ellemenno/pinwheel-system/wing5-2.stl

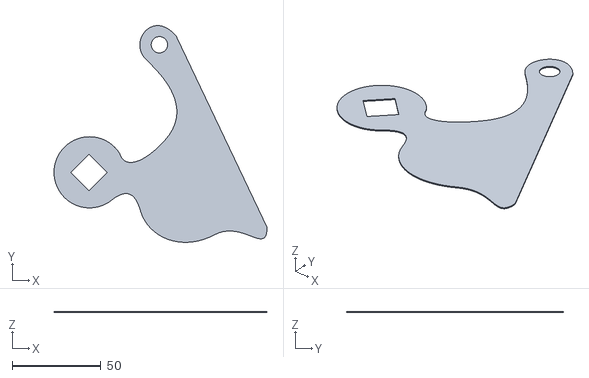
[picture p14: CAD file, 2023-04-02]
wing5-2.stl
119.9 x 122.0 x 0.5
