ellemenno/pinwheel-system/housing+fin.stl

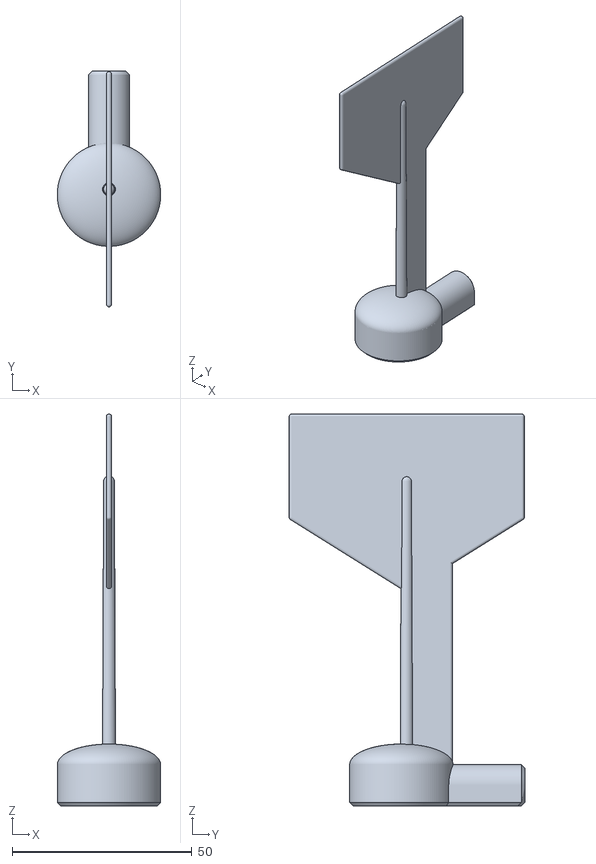
[picture p15: CAD file, 2023-04-02]
housing+fin.stl
28.8 x 65.6 x 109.1
