ellemenno/pinwheel-system/pin6.stl

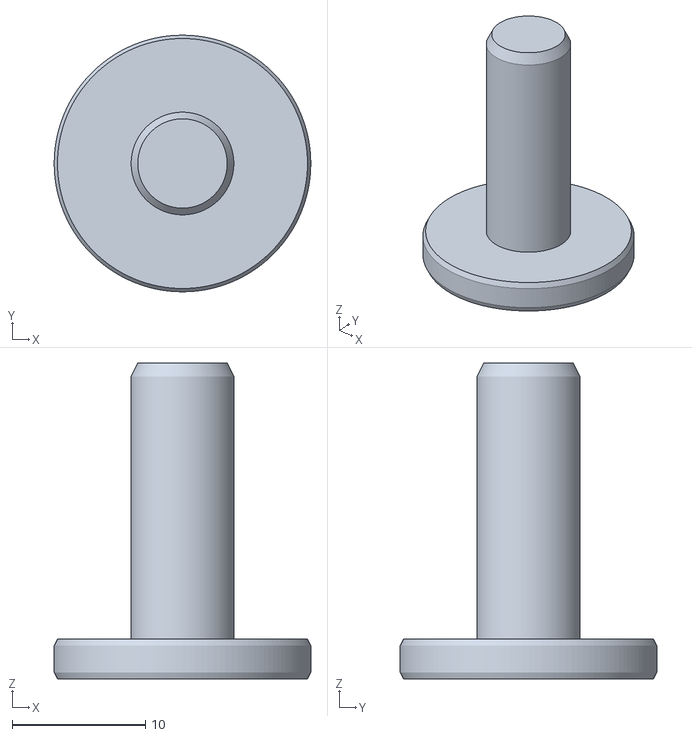
[picture p16: CAD file, 2023-04-02]
pin6.stl
19.2 x 19.2 x 23.7
